rstms68/BeoControl/BeoIREye/BeoButton.h

/*
  BeoButton.h - Library for IR eye button handling.
  Created by styppen.
*/

#include "Arduino.h"
#include "PCF8574.h"


class BeoButton
{
  public:
    BeoButton(int pcfPin, String type);
    BeoButton(String type);

    static void updateLed(PCF8574& pcf, int pin, int state);
     void update(PCF8574& pcf, int state);
    void update(int state);
  private:
    boolean previousState = HIGH;
    unsigned long pressStart;
    int currentState;
    String msg;
    char payload[20];
 
    String buttonType;
    int pin;


};
